UU5JPP/ViktoRi_ZU/Схемы и платы/1.jpg

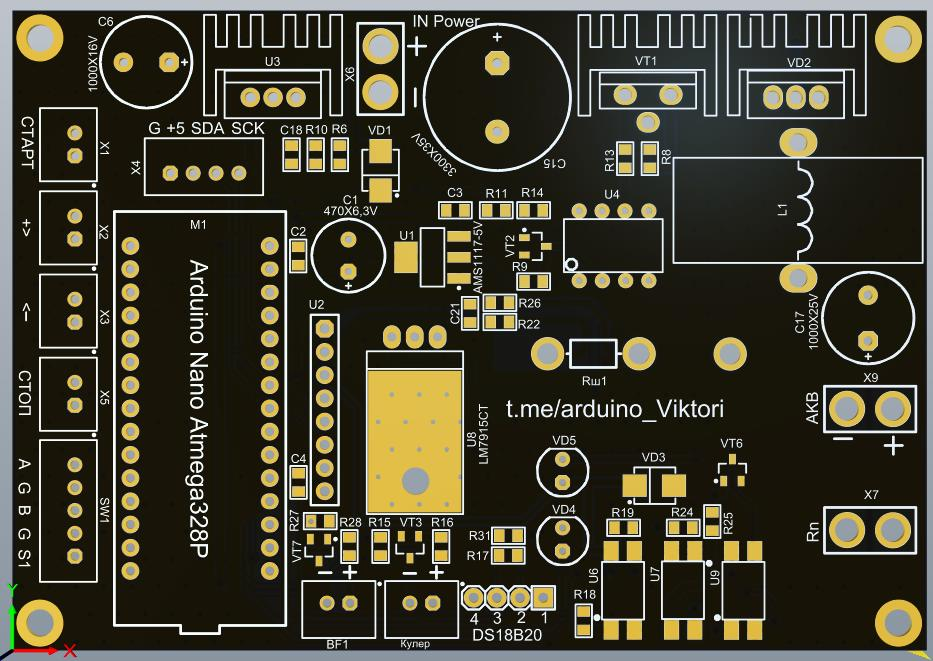
Схемы и платы/1.jpg
