UU5JPP/ViktoRi_ZU/Схемы и платы/2.jpg

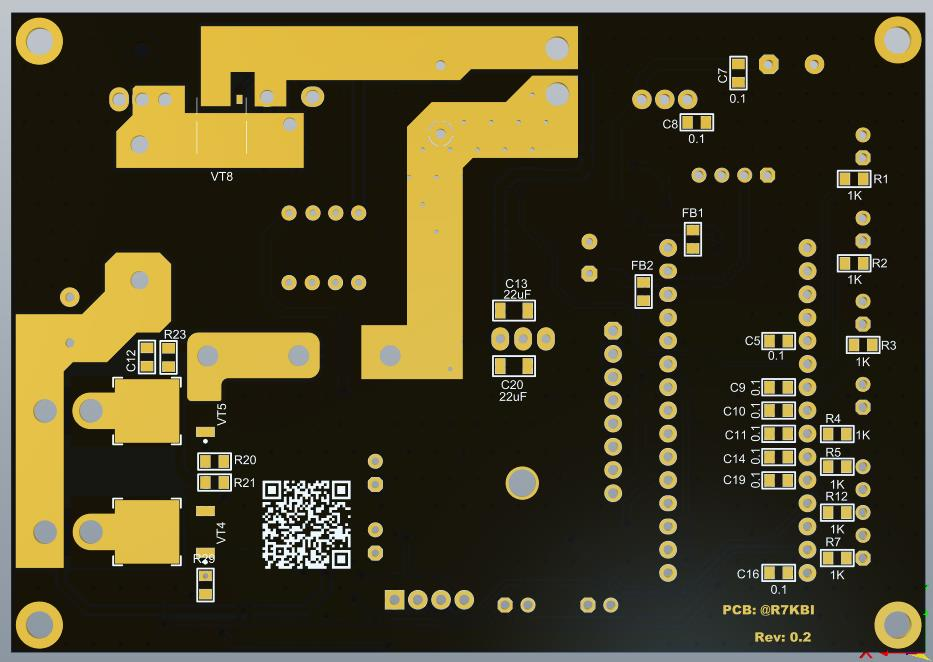
Схемы и платы/2.jpg
