UU5JPP/ViktoRi_ZU/Схемы и платы/4.jpg

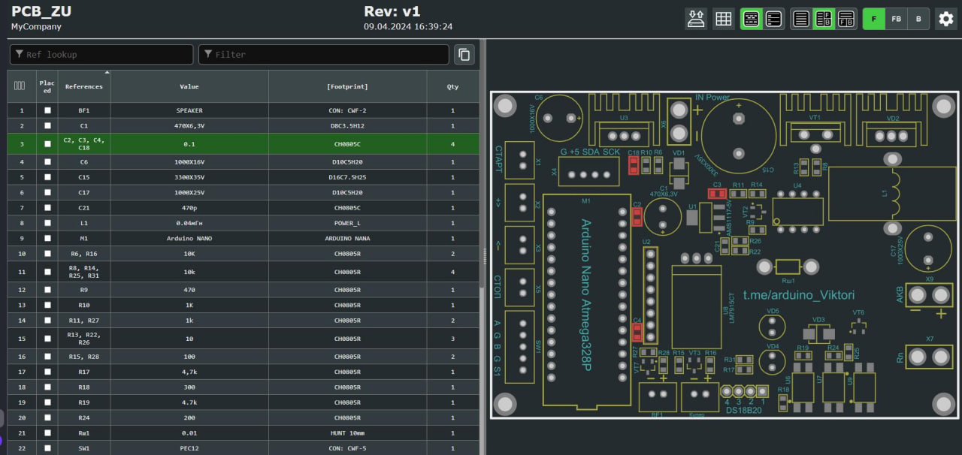
Схемы и платы/4.jpg
