UU5JPP/ViktoRi_ZU/Исходники arduino/ViktoRi_ver_1_32_test_1/z_function.ino

// постоянно работающие функции
void sensor_survey(void) {
  butt.Tick();  // опрос кнопок и энкодера

  if (ina.sample()) {
    dcdc.Control();  // регулировка тока и напряжения
#if (VOLTIN == 1)    // напряжение от БП
    check_Q1();      //проверка на то что силовой транзистор пробит
#endif
#if (VOLTIN == 1)
    adc.check();   // проверить напряжение на превышение
#endif
  }

#if (VOLTIN == 1)
  adc.sample();  // чтение сырых данных с аналогового пина с усреднением - напряжения БП
#endif

  if (sekv.tick()) {
    // выполняются раз в секунду
#if (VOLTIN == 1 or SENSTEMP1 == 2 or SENSTEMP2 == 2)
    adc.compute();  // Вызывается раз в секунду или реже.
#endif
#if (SENSTEMP2 == 1)
    akb.read_temp();  // чтение датчика температуры акб DS18B20
#endif

    kul.fan();  // чтение температуры и управение кулером
#if (POWPIN == 1)
    Relay();  // функция управления реле подключения к сети 220В
#endif
  }
}


// функция хранения акб и буферного режима
void Storage(bool regim) {
  bool ext = true;
  bool vvmin = true;                       // флаг отключения нагрузки
  uint32_t t_st = 0;                       // время хранения
  uint8_t sig = 0;                         // время отстчета сигнала буферного режима
  uint16_t vbc = bat.Volt(3) / 100 * 100;  // расчет напряжения - снижение до 12В
#if (GUARDA0)
  Guard();  // принудительная блокировка модуля защиты при напряжении заряда или разряда акб менее 5 Вольт.
#endif
#if (POWPIN == 1)
  gio::high(RELAY220);               // включить сеть 220В
  bitClear(flag_global, RELEY_OFF);  // запрещено отключать реле
#endif
  Freq(EEPROM.read(8 + FREQCHARGE));  // установить частоту работы силового модуля
  {
    int16_t amp = (regim ? (constrain(pam.Capacity << 2, 50, 1000)) : pam.Current_charge);  // максимальный ток заряда
    uint16_t vlt = regim ? pam.Volt_storage : pam.Volt_buffer;
    PrintVA(vlt, amp, 0, 0, 1);  // вывод напряжения и тока заряда
    Delay(3000);
    dcdc.begin(vlt, amp);  // задать максимальные значения напряжения и тока заряда
  }
  if (!regim) gio::high(PIN_13);  // включить пин 13. Включить реле нагрузки
  sekd.start();                   // старт отсчета времени одна секунда
  ina.start(1);                   // старт замеров INA
  dcdc.start(DCDC_CHARGE);
  while (ext) {
    // цикл работы
    sensor_survey();                                                 // опрос кнопок, INA226, напря. от БП., контроль dcdc.
    if (butt.tick == ENCHELD or butt.tick == STOPHELD) ext = false;  // завершить заряд

    // если прошла секунда
    if (sekd.tick()) {
#if (GUARDA0)
      Guard();  // принудительная блокировка модуля защиты при напряжении заряда или разряда акб менее 5 Вольт.
#endif
      Print_time(t_st++, DISPLAYx - 8, 0);          // *Storage 12:10:36*
      setCursory();                                 // *13.10V 6.12A 25C*
      PrintVA(ina.voltsec, ina.ampersec, 0, 0, 2);  // вывод на дисплей во float - напряжение, ток, ампер-часы, ватт-часы, кол. разрядов после запятой.
#if (SENSTEMP1 or SENSTEMP2)
      print_tr();  // температура транзистора или акб
#endif

      // сигнализация о снижении напряжения акб ниже предела (12V)
      if (ina.voltsec < vbc) {
        if (!sig) {
#if (TIME_LIGHT)
          disp.Light_high();  // включение подсветки
#endif
          Speaker(300);  // функция звукового сигнала (время в миллисекундах)
          sig = 60;      // сигнал раз в 60 секунд
        } else sig--;

        if (!regim) {
          // включен буферный режим
          if (vvmin and ina.voltsec < bat.Volt(3)) {
            // если нагрузка подключена и напряжение снизилось менее напряжения разряда то
            Speaker(300);  // функция звукового сигнала (время в миллисекундах)
            vvmin = false;
            gio::low(PIN_13);  // отключить пин 13. отключить реле нагрузки
          }
        }
      }
      if (!vvmin and ina.voltsec > pam.Volt_buffer - 200) {
        // когда реле нагрузки отключено и напряжение увеличилось до максимального то
        Speaker(300);  // функция звукового сигнала (время в миллисекундах)
        vvmin = true;
        gio::high(PIN_13);  // включить пин 13. отключить реле нагрузки
      }
#if (TIME_LIGHT)
      if (!regim) disp.Light_low();  // отключение подсветки через 3 минуты в буферном режиме, если разрешено отключение
#endif
#if (LOGGER)
      Sout.Serial_out();
#endif
    }
    // если прошла секунда
  }
  // цикл работы
  gio::low(PIN_13);  // отключить пин 13. отключить реле нагрузки
  dcdc.Off();        // отключить заряд, разряд.
#if (GUARDA0)
  gio::low(PINA0);  // отключить блокировку модуля защиты
#endif
}

// расчет токов и напряжений
void calculate(uint8_t i) {
  switch (i) {
    case 1:
      pam.Current_charge = constrain(bat.Cur(0), CUR_CHARGE_MIN, CURRMAXINT);       // ток заряда
      pam.Current_charge_min = constrain((int16_t)pam.Capacity << 1, CURMIN, 200);  // ток завершения заряда
      pam.Current_discharge = constrain(bat.Cur(2), 50, CURRMAXINT);                // ток разряда
      pam.Current_discharge_min = pam.Current_discharge;                            // ток завершения разряда
      pam.Current_add_charge = constrain(bat.Cur(1), CUR_CHARGE_MIN, CURRMAXINT);   // ток дозаряда
      pam.Current_add_charge_min = pam.Current_add_charge / 3;                      // минимальный ток дозаряда
      pam.Current_pre_charge = constrain(pam.Current_charge / 3, 200, CURRMAXINT);  // ток предзаряда
      ChargeTimeCalc();                                                             // расчет времени заряда
      pam.Round = 1;                                                                // 1 раунд
      break;
    case 2:
      // расчет напряжений
      {
        pam.Volt_charge = bat.Volt(1);     // напряжение заряда, напряжение заряда ячейки на количество ячеек
        pam.Volt_decrCur = Volt_DCur();    // напряжение при котором начинается снижение тока заряда
        pam.Volt_discharge = bat.Volt(3);  // напряжение разряда
        uint16_t vbc = bat.Volt(0);
        pam.Volt_storage = (uint16_t)(vbc * 1.04f);      // напряжение хранения
        pam.Volt_buffer = (uint16_t)(vbc * 1.1f);        // напряжение буферного режима
        if (pam.typeAkb < 5) {                           // расчет для свинцово кислотных Акб
          pam.Volt_add_charge = bat.Volt(2);             // напряжение дозаряда
          pam.Volt_pre_charge = (uint16_t)(vbc * 1.1f);  // напряжение предзаряда
        }
      }
      break;
  }
}

#if (POWPIN == 1)
// функция управления реле подключения к сети 220В
void Relay(void) {
  if (ina.voltsec < 9000) {
    // если напряжение подключенной АКБ ниже 9 вольт включается реле 220В.
    gio::high(RELAY220);                                                           // включить питание реле (подкл. питание от сети 220В)
    tvin.start();                                                                  // запомнить время
  } else if (bitRead(flag_global, RELEY_OFF) and tvin.tick()) gio::low(RELAY220);  // если разрешено отключать реле и прошло 2 минуты то отключить питание реле (откл. питание от сети 220В)
}
#endif

// функция расчета Ач и Втч
int32_t aw_ch(int32_t i) {
  return (i * 100 / 3600);
}

// функция включения блокировки модуля защиты в зависимости от напряжения акб
// включает блокировку при напряжении акб менее 5 Вольт и отключает при напр. более 6 Вольт
#if (GUARDA0)
void Guard(void) {
  if (ina.voltsec < 5000) gio::high(PINA0);
  else if (ina.voltsec > 6000) gio::low(PINA0);
}
#endif

// функция сброса значений заряда
void Res_mem_char(void) {
  pam.Ah_charge = 1;  // единица для того чтобы Ач и Вт сразу отображались на дисплее
  pam.Wh_charge = 1;
  pam.Time_charge = 0;
  pam.Time_addcharge = 0;
  pam.Ah_addcharge = 0;
  pam.Wh_addcharge = 0;
#if (BRANIMIR == 1)
  bitClear(pam.MyFlag, BRANIM);
  bitClear(pam.MyFlag, BRANIMBOIL);
#endif
}

// функция сброса значений разряда
void Res_mem_dischar(void) {
  pam.Ah_discharge = 1;    // емкость разряда Ah  // единица для того чтобы Ач и Вт сразу отображались на дисплее
  pam.Wh_discharge = 1;    // емкость разряда Вт/ч
  pam.Time_discharge = 0;  // время разряда
  pam.Ah_addcharge = 0;    // емкость разряда до напряжения аккумулятора
  pam.Wh_addcharge = 0;    // емкость до напряжения аккумулятора Вт/ч
}

// очистить память значений КТЦ
void Res_ktc(void) {
  EEPROM.put((MEM_KTC - 1), pam.Round);                         // сохранить количество циклов
  for (uint16_t i = MEM_KTC; i <= 1019; i++) EEPROM.put(i, 0);  // очистить память КТЦ
}

// функция ожидания (t - милисекунды)
void Delay(uint16_t t) {
  uint32_t r = millis();
  do {
    sensor_survey();  // опрос кнопок, INA226, напря. от БП., контроль dcdc.  // and !butt.tick
  } while ((millis() - r < t) and !butt.tick);
}

// пауза до нажатия
void pauses(void) {
  do {
    sensor_survey();  // опрос кнопок, INA226, напря. от БП., контроль dcdc.
  } while (!butt.tick);
}

// напряжение при котором начинается снижение тока заряда
uint16_t Volt_DCur(void) {
  return (pam.Volt_charge + bat.Volt(0)) >> 1;
}


// калибровка падения напряжения при токе нагрузки, напряжения от БП
void Korrect(const uint8_t kof) {
  if (kof and !VOLTIN) return;  // если выбрана калибровка напряжения от БП и не установлен делитель напряжения на входе то выйти из функции

#if (TIME_LIGHT)
  disp.Light_high();  // включение подсветки
#endif
  if (!kof) {
#if (GUARDA0)
    Guard();  // принудительная блокировка модуля защиты при напряжении заряда или разряда акб менее 5 Вольт.
#endif
    ina.start(2);  // старт замеров INA
    while (ina.voltsec < 9000) {
      lcd.clear();
      lcd.print(F(txt11));   //  Подключи АКБ
      lcd.print(F(" >9V"));  //
      Delay(200);
      if (butt.tick == STOPCLICK or butt.tick == ENCCLICK) {
        dcdc.Off();
        return;
      }
    }
    Freq(EEPROM.read(8 + FREQDISCHAR));    // установить частоту работы разрядного модуля (4 кГц по умолчанию)
    bitSet(pam.MyFlag, CHARGE);            // старт работы режима
    dcdc.start(DCDC_DISCHARGE);            // настройка разряда
    dcdc.Smooth_off();                     // отключить плавный пуск
    dcdc.begin((ina.voltsec >> 1), 2100);  // задает напряжение и ток разряда
    lcd.clear();
  } else {
#if (POWPIN == 1)
    gio::high(RELAY220);               // включить сеть 220В
    bitClear(flag_global, RELEY_OFF);  // запрещено отключать реле
#endif
    lcd.clear();
  }
  bool x = false;
  bool ext = true;
  sekd.start();  // старт отсчета времени
  do {
    // установка напряжения
    do {
      // ожидание действий пользователя
      sensor_survey();                                                  // опрос кнопок, INA226, напря. от БП., контроль dcdc.
      if (!kof and ina.ampersec < -2000) bitClear(pam.MyFlag, CHARGE);  // отключить стабилизацию тока
      if (sekd.tick() or butt.tick) {
        // вывод на дисплей
        switch (kof) {
          case 0:
            setCursorx();  // 0, 0
            PrintVA(ina.voltsec, ina.ampersec, 0, 0, 3);
            if (BitIsClear(pam.MyFlag, CHARGE)) {
              setCursory();  // *12.365V 3.254А  *
              Write_x(x);    // > or  пробел  // *>80     >55    *
              lcd.print(vkr.Ohms);
              printSimb();
              lcd.setCursor(8, 1);
              Write_x(!x);  // > or  пробел
              lcd.print(((float)vkr.shunt / 100));
              lcd.print(F("mOm "));
            }
            break;
#if (VOLTIN == 1)
          case 1:
            // замер напряжения блока питания
            setCursorx();
            PrintVA(adc.volt, 0, 0, 0, 2);
            lcd.write('<');  // <
            lcd.print(vkr.Vref);
            lcd.write('>');  // >
            break;
#endif
        }
      }
    } while (!butt.tick);

    switch (butt.tick) {
      if (BitIsClear(pam.MyFlag, CHARGE)) {
        case ENCCLICK:
        case OKCLICK:
          x = !x;
          break;
        case RIGHT:
        case LEFT:
          switch (kof) {
            case 0:
              if (x) vkr.Ohms = constrain(vkr.Ohms + butt.tick, 0, 255);
              else vkr.shunt = constrain(vkr.shunt + butt.tick, 10, 10000);  // 1 - 0,1 мОм, 10000 - 100мОм
              ina.start(2);                                                  // старт замеров INA
              break;
              // замер напряжения блока питания
#if (VOLTIN == 1)
            case 1:
              vkr.Vref = constrain(vkr.Vref + butt.tick, 1000, 6000);
              break;
#endif
          }
          break;
      }
      case ENCHELD:
      case STOPCLICK:
        ext = false;
        break;
    }
  } while (ext);  // установка напряжения
  dcdc.Off();     // отключить заряд, разряд.
  bitClear(pam.MyFlag, CHARGE);
  EEPROM.put(1, vkr);
#if (POWPIN == 1)
  bitSet(flag_global, RELEY_OFF);  // разрешено отключать реле
#endif
}


// Функция ожидания time_charge - минут
void Wait(uint16_t time_charge) {
#if (POWPIN == 1)
  bitSet(flag_global, RELEY_OFF);  // разрешено отключать реле
#endif
  lcd.clear();
  lcd.print(F(txt16));  // Pause
  uint8_t tm = 60;
  sekd.start();  // старт отсчета времени одна секунда
  ina.start(2);  // старт замеров INA
  do {
    sensor_survey();  // опрос кнопок, INA226, напря. от БП., контроль dcdc.

    // если прошла секунда вывод на дисплей
    if (sekd.tick()) {
      setCursory();
      PrintVA(ina.voltsec, 0, 0, 0, 2);
      lcd.print(time_charge);
      lcd.print(F(txt20));  // "мин"
      tm--;
      if (!tm) {
        // когда прошла минута
        tm = 60;
        time_charge--;
      }
#if (LOGGER)
      Sout.Serial_out();
#endif
#if (TIME_LIGHT)
      disp.Light_low();  // отключение подсветки через 3 минуты, если разрешено отключение
#endif
    }
  } while (time_charge and butt.tick != STOPHELD and butt.tick != ENCHELD);  //  цикл в минутах или долгово нажатия OK
}

// Функция завершения заряда
void End(void) {
  lcd.clear();
  lcd.print(regim_end);  // вывод причины завершения работы.
  printSimb();           // пробел
  print_mode(0);         // вывод режима
  setCursory();
  int32_t Ah;
  uint32_t tm;
  switch (pam.Mode) {
    case 0:
      // Заряд
      Ah = pam.Ah_charge;
      tm = pam.Time_charge;
      break;
    case 1:
    case 2:
    case 5:
      // Заряд-Дозаряд , Бранимир, КТЦ
      Ah = pam.Ah_charge + pam.Ah_addcharge;
      tm = pam.Time_charge + pam.Time_addcharge;
      break;
    case 3:
      // Дозаряд
      Ah = pam.Ah_addcharge;
      tm = pam.Time_addcharge;
      break;
    case 4:
      // Разряд
      Ah = pam.Ah_discharge;
      tm = pam.Time_discharge;
      break;
    case 6:
    case 7:
      // Хранение, Буфер.
      Ah = 0;
      tm = 0;
      break;
  }
  PrintVA(0, 0, Ah, 0, 2);
#if (DISPLAYx == 16)
  Print_time(tm, DISPLAYx - 5, 1);
#elif (DISPLAYx == 20)
  Print_time(tm, DISPLAYx - 11, 1);
#endif
#if (DISPLAYy == 4)
  lcd.setCursor(0, 2);
  ClearStr(3);
#endif
  regim_end = 0;
  Speaker(1000);  // функция звукового сигнала (время в миллисекундах)
  Delay(1000);    // подождать
  pauses();       // пауза до нажатия
  lcd.clear();    // очистить дисплей
  Delay(500);     // подождать
}

// функция выбора Stop/OK. (timer - секунд, время через которое возвращается false. Если timer = 0 то возврат из функции по нажатию кнопок/енкодера)
bool Choice(uint8_t secund, bool rez) {
  sekd.start();
  sensor_survey();  // опрос кнопок, INA226, напря. от БП., контроль dcdc.
  do {
    switch (butt.tick) {
      case LEFT:
      case RIGHT:
        rez = !rez;
        break;
      case ENCCLICK:
      case OKCLICK:
      case STOPCLICK:
        return rez;
        break;
    }
    lcd.setCursor(4, 1);
    lcd.print((rez ? F(txt17) : F(txt19)));  // OK / Stop

    do {
      // цикл ожидания действий пользователя
      sensor_survey();  // опрос кнопок, INA226, напря. от БП., контроль dcdc.
      if (sekd.tick()) {
        // если прошла секунда вывод на дисплей
        lcd.setCursor(DISPLAYx - 2, 1);
        lcd.print(secund);
        printSimb();
        secund--;
      }
    } while (!butt.tick and secund);  // цикл ожидания действий пользователя
  } while (secund);                   // ожидание истечения времени
  return rez;
}


// функция звукового сигнала (n - время в миллисекундах)
void Speaker(uint16_t n) {
// активный звукового сигнала
#if (SPEAKER == 2)
  gio::high(BUZER);  // включить сигнал
  Delay(n);          // подождать n - миллисекунд
  gio::low(BUZER);   // отключить сигнал

#elif (SPEAKER == 1)
  // пассивный звукового сигнала
  uint32_t time2 = millis();
  // звуковой сигнал в течении n миллисекунд
  while (millis() - time2 < n) {
    gio::high(BUZER);        // HIGH
    delayMicroseconds(300);  // 2314 - частота 432Гц; 1157 - частота 864Гц; 771 - частота 1296Гц
    gio::low(BUZER);         // LOW
    delayMicroseconds(471);
  }
#endif
  return;
}

// расчет времени заряда
void ChargeTimeCalc(void) {
  uint8_t v = (uint8_t)((uint32_t)pam.Capacity * 1000 / pam.Current_charge);
  pam.Time_charge_h = constrain(v + ((v + 2 - 1) >> 1), 1, 100);  // расчет времени заряда
}

// вычисление процента заряда (максим напряж заряда,текущее напряжение заряда, текущий ток заряда, минимальный ток заряда)
uint8_t Percentage(uint16_t volt_max, uint16_t volt, int16_t current, int16_t curr_min) {
  uint16_t vmin = bat.Volt(3);                       // миним напряжение (напряжение разряда)
  if (volt < vmin) return 0;                         // если текущее напряжение акб меньше напряжения разряда то вернуть 0%
  uint8_t vperc = map(volt, vmin, volt_max, 1, 50);  // процент заряда по напряжению 50%
  vperc += (uint8_t)(curr_min * 50 / current);       // прибавляем процент заряда по току 50%
  return constrain(vperc, 1, 100);
}

#if (CORRECTCUR == 1 and SENSTEMP2 == 2)
// контроль температуры Акб с датчика NTC подключенного к пин А6 Ардуино
void Control_trAkb(void) {
  if (bitRead(flag_global, TEMP_AKB)) {
    if (adc.tmp_akb > 40) bitClear(flag_global, TEMP_AKB);
    else if (pam.typeAkb <= 4 and adc.tmp_akb < -15) bitClear(flag_global, TEMP_AKB);
    else if ((pam.typeAkb <= 6 or pam.typeAkb == 8) and adc.tmp_akb < 10) bitClear(flag_global, TEMP_AKB);
  }

  if (BitIsClear(flag_global, TEMP_AKB)) {
    dcdc.stop();  // остановить заряд
#if (TIME_LIGHT)
    disp.Light_high();  // включение подсветки
#endif
    lcd.clear();
    lcd.print(F(txt9));  // "Temp akb:"
    Speaker(1000);       // функция звукового сигнала (время в миллисекундах)
    uint32_t sek = 0;
    do {
      sensor_survey();  // опрос кнопок, INA226, напря. от БП., контроль dcdc.  // and !butt.tick
      if (butt.tick == ENCHELD or butt.tick == STOPHELD) {
        bitClear(pam.MyFlag, CHARGE);
        return;
      }
      if (millis() - sek >= 3000) {
        sek = millis();
        lcd.setCursor(9, 0);
        lcd.print(adc.tmp_akb);
        printSimb();  // пробел
        setCursory();
        PrintVA(ina.voltsec, ina.ampersec, 0, 0, 3);

        if (adc.tmp_akb < 37) {
          if (pam.typeAkb <= 4 and adc.tmp_akb > -14) bitSet(flag_global, TEMP_AKB);
          else if ((pam.typeAkb <= 6 or pam.typeAkb == 8) and adc.tmp_akb > 11) bitSet(flag_global, TEMP_AKB);
        }
      }
    } while (BitIsClear(flag_global, TEMP_AKB));
    lcd.clear();
    Speaker(1000);  // функция звукового сигнала (время в миллисекундах)
  }
}
#endif

#if (CORRECTCUR == 1 and SENSTEMP2 == 1)
// контроль температуры Акб с датчика NTC подключенного к пин А6 Ардуино
void Control_trAkb(void) {
  if (bitRead(flag_global, TEMP_AKB)) {
    if (akb.temp > 40) bitClear(flag_global, TEMP_AKB);
    else if (pam.typeAkb <= 4 and akb.temp < -15) bitClear(flag_global, TEMP_AKB);
    else if ((pam.typeAkb <= 6 or pam.typeAkb == 8) and akb.temp < 10) bitClear(flag_global, TEMP_AKB);
  }

  if (BitIsClear(flag_global, TEMP_AKB)) {
    dcdc.stop();  // остановить заряд
#if (TIME_LIGHT)
    disp.Light_high();  // включение подсветки
#endif
    lcd.clear();
    lcd.print(F(txt9));  // "Temp akb:"
    Speaker(1000);       // функция звукового сигнала (время в миллисекундах)
    uint32_t sek = 0;
    do {
      sensor_survey();  // опрос кнопок, INA226, напря. от БП., контроль dcdc.  // and !butt.tick
      if (butt.tick == ENCHELD or butt.tick == STOPHELD) {
        bitClear(pam.MyFlag, CHARGE);
        bitSet(flag_global, TEMP_AKB);
        return;
      }
      if (millis() - sek >= 3000) {
        sek = millis();
        lcd.setCursor(9, 0);
        lcd.print(akb.temp);
        printSimb();  // пробел
        setCursory();
        PrintVA(ina.voltsec, ina.ampersec, 0, 0, 3);

        if (akb.temp < 37) {
          if (pam.typeAkb <= 4 and akb.temp > -14) bitSet(flag_global, TEMP_AKB);
          else if ((pam.typeAkb <= 6 or pam.typeAkb == 8) and akb.temp > 11) bitSet(flag_global, TEMP_AKB);
        }
      }
    } while (BitIsClear(flag_global, TEMP_AKB));
    lcd.clear();
    Speaker(1000);  // функция звукового сигнала (время в миллисекундах)
  }
}
#endif

#if (VOLTIN == 1)  // напряжение от БП

//проверка на то что силовой транзистор пробит
void check_Q1(void) {
  if ((abs((int16_t)ina.voltms - (int16_t)adc.volt) < 100) and ina.amperms > 100) {
#if (TIME_LIGHT)
    disp.Light_high();  // включение подсветки
#endif
    bitSet(vkr.GlobFlag, TRQ1);
    dcdc.Off();
#if (GUARDA0)
    gio::low(PINA0);  // разблокировать защитный модуль
#endif
#if (PROT == 1)
    gio::low(PROTECT);  //закрыть защитный транзистор
#endif
#if (POWPIN == 1)
    gio::low(RELAY220);  // отключить сеть 220В
#endif

    Saved();  // сохранить настройки
    lcd.clear();
    lcd.print(F(txt24));  //"!!-BROKEN Q1-!!"

    pauses();

    bitClear(vkr.GlobFlag, TRQ1);  // при нажатии записать в память что транзистор исправен
    Saved();                       // сохранить настройки
#if (PROT == 1)
    gio::low(PROTECT);  // открыть защитный транзистор Q4
#endif
#if (POWPIN == 1)
    gio::high(RELAY220);  // включить сеть 220В
#endif
#if (GUARDA0)
    Guard();  // принудительная блокировка модуля защиты при напряжении заряда или разряда акб менее 5 Вольт.
#endif
    lcd.clear();
  }
}
#endif

/*
// ===================== FLAGS Button======================
#define EB_PRESS (1 << 0)       1 // нажатие на кнопку
#define EB_HOLD (1 << 1)        2 // кнопка удержана
#define EB_STEP (1 << 2)        4 // импульсное удержание
#define EB_RELEASE (1 << 3)     8 // кнопка отпущена
#define EB_CLICK (1 << 4)       16 // одиночный клик
#define EB_CLICKS (1 << 5)      32 // сигнал о нескольких кликах
#define EB_TURN (1 << 6)        64 // поворот энкодера
#define EB_REL_HOLD (1 << 7)    128 // кнопка отпущена после удержания
#define EB_REL_HOLD_C (1 << 8)  256 // кнопка отпущена после удержания с предв. кликами
#define EB_REL_STEP (1 << 9)    512 // кнопка отпущена после степа
#define EB_REL_STEP_C (1 << 10) 1024 // кнопка отпущена после степа с предв. кликами

// ===================== FLAGS Encoder======================
#define EB_TYPE (1 << 0)
#define EB_REV (1 << 2)
#define EB_FAST (1 << 3)
#define EB_EHLD_M (1 << 4)
#define EB_DIR (1 << 5)
#define EB_ETRN_R (1 << 6)
#define EB_ISR_F (1 << 7)
*/
